Fmulder007/Karat2N_synt/1freq/tiny13synt1785/2023-01-13_09-19-21.jpg

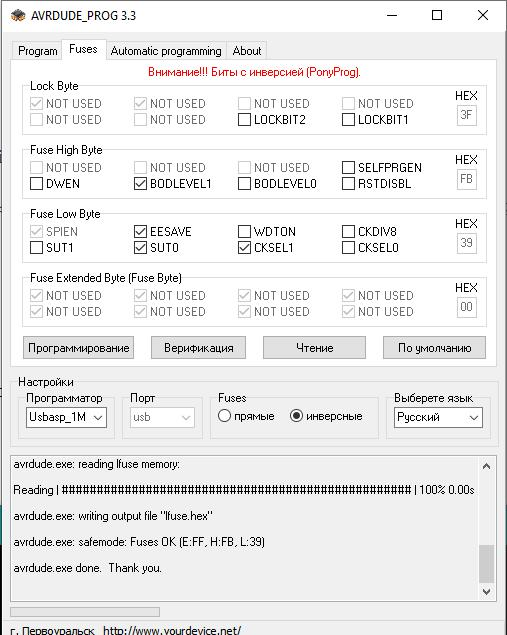
1freq/tiny13synt1785/2023-01-13_09-19-21.jpg
