Fmulder007/Karat2N_synt/3D stuff/2021-10-06_18-04-43.jpg

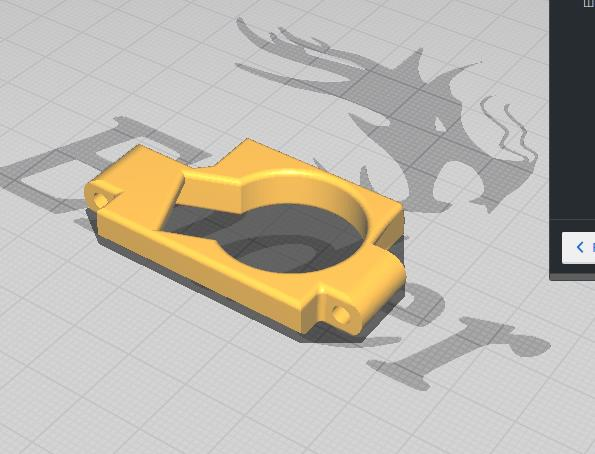
3D stuff/2021-10-06_18-04-43.jpg
