Fmulder007/Karat2N_synt/3D stuff/Conduktor.jpg

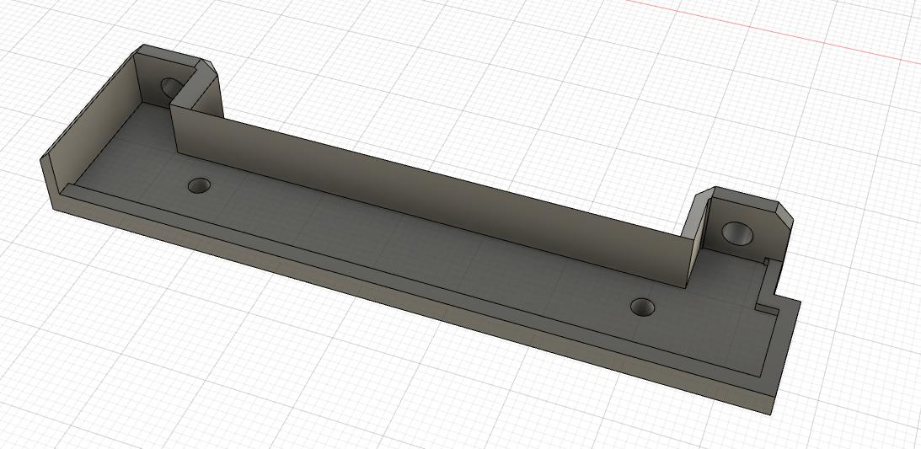
3D stuff/Conduktor.jpg
