Fmulder007/Karat2N_synt/3D stuff/photo_2021-10-07_09-59-49.jpg

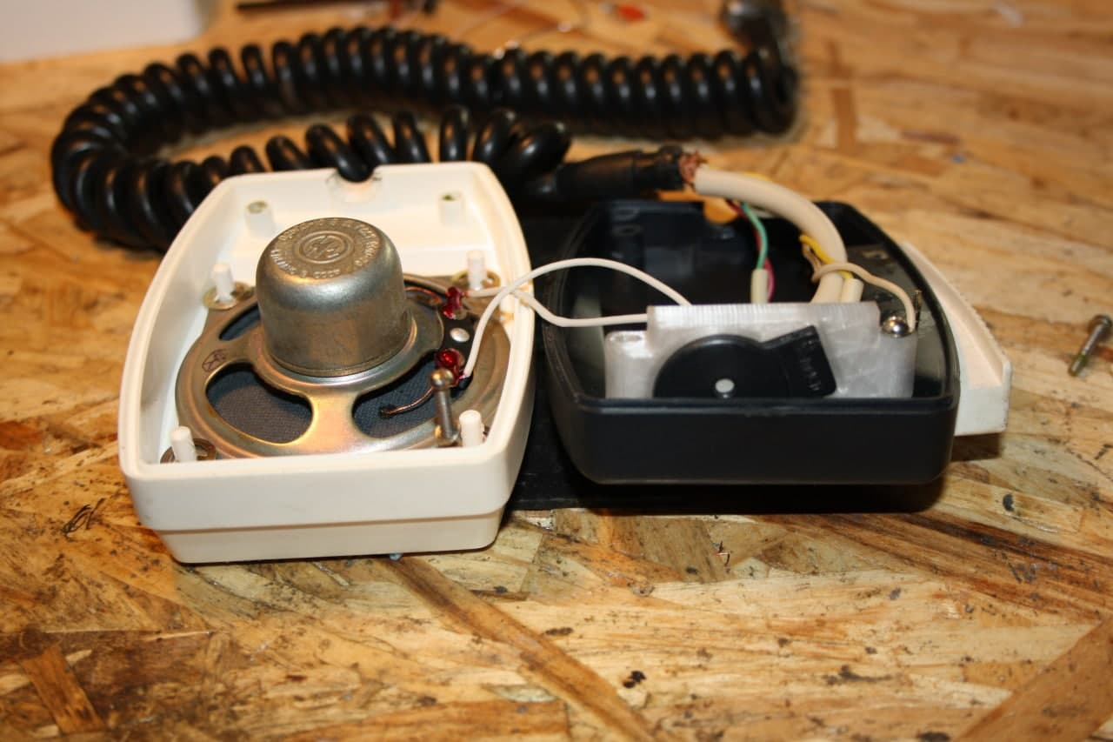
3D stuff/photo_2021-10-07_09-59-49.jpg
