Fmulder007/Karat2N_synt/3D stuff/RTC_Support.jpg

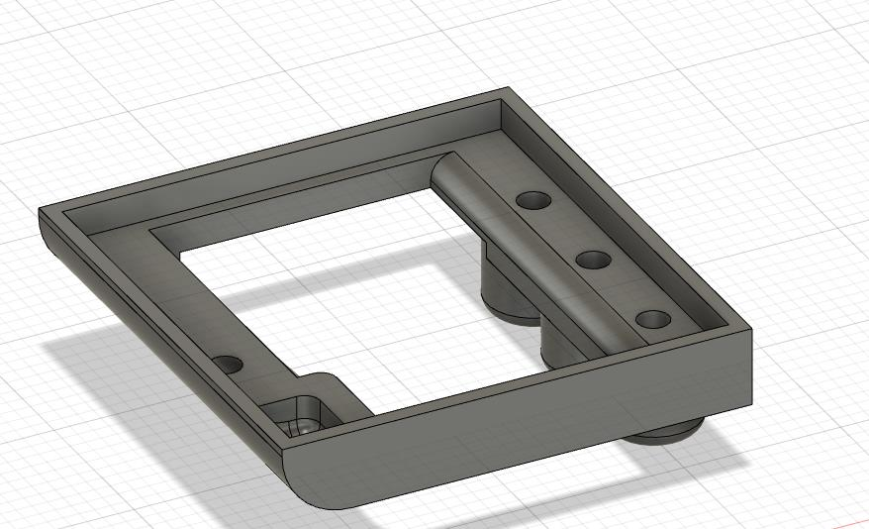
3D stuff/RTC_Support.jpg
