Fmulder007/Karat2N_synt/2021-10-20_19-13-40.jpg

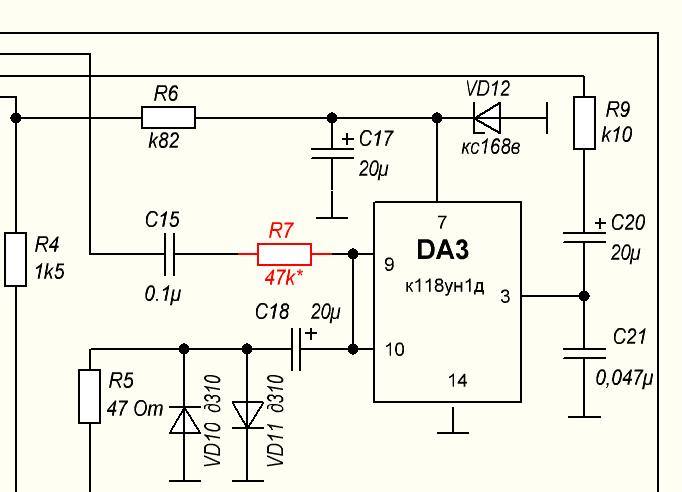
2021-10-20_19-13-40.jpg
