Fmulder007/Karat2N_synt/2021-10-20_19-15-04.jpg

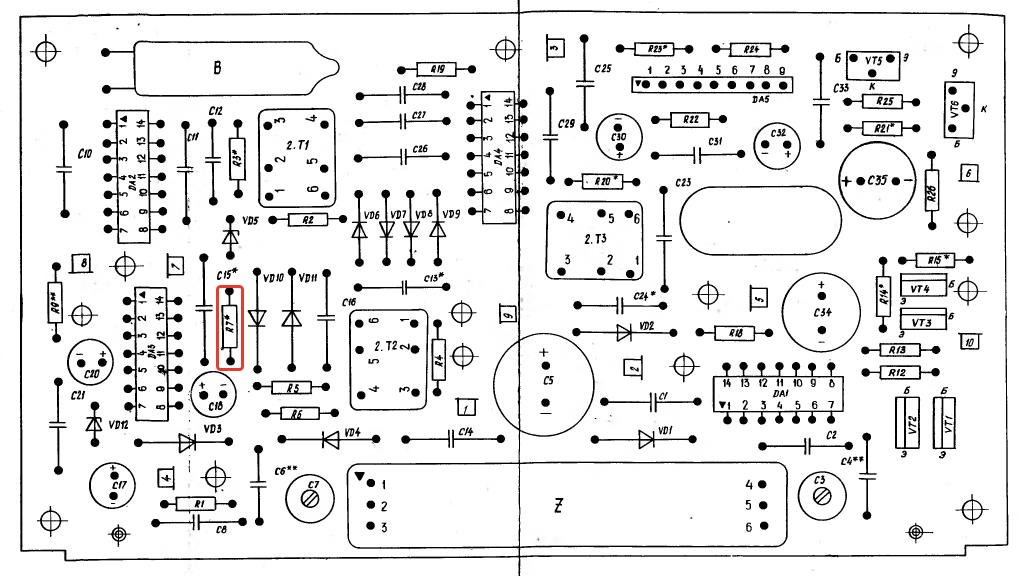
2021-10-20_19-15-04.jpg
