Fmulder007/Karat2N_synt/2022-11-13_21-02-55.jpg

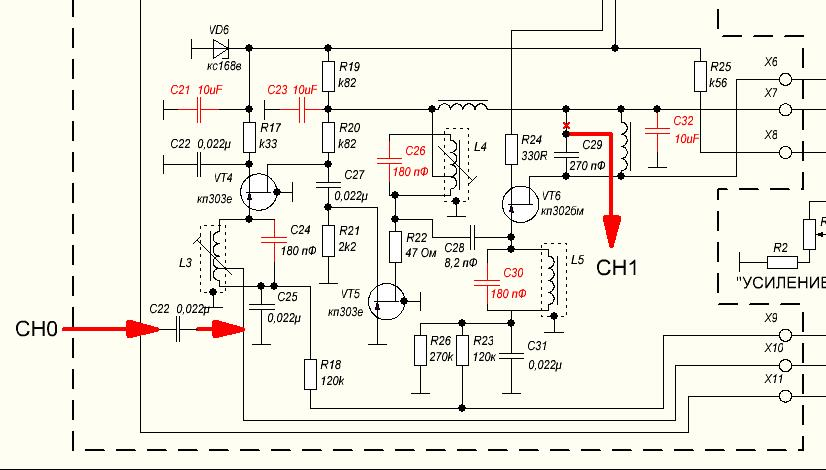
2022-11-13_21-02-55.jpg
