Fmulder007/Karat2N_synt/ANT.GIF

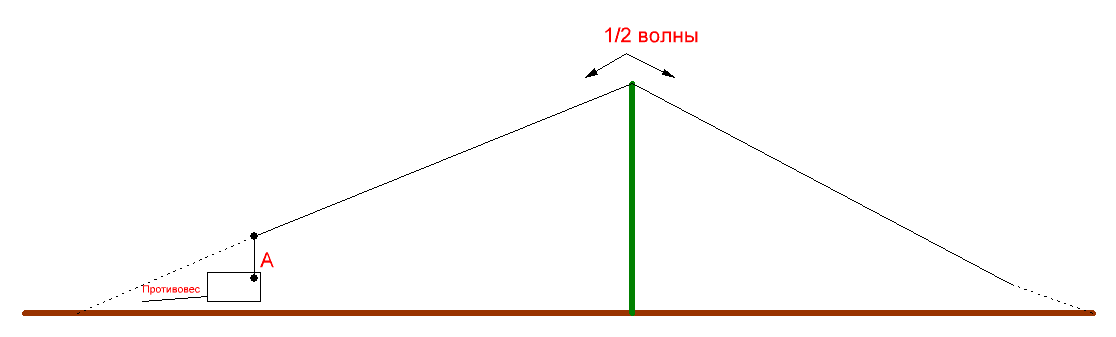
ANT.GIF
