Fmulder007/Karat2N_synt/DEMSH.GIF

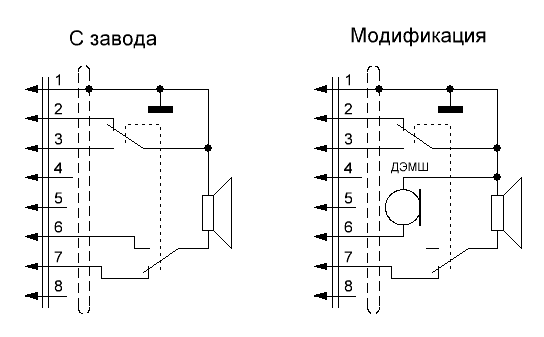
DEMSH.GIF
