Fmulder007/Karat2N_synt/Driver.GIF

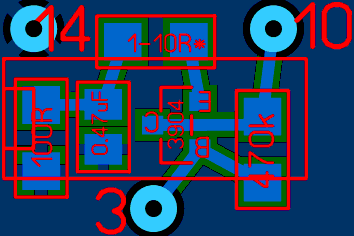
Driver.GIF
