Fmulder007/Karat2N_synt/DriverSch.GIF

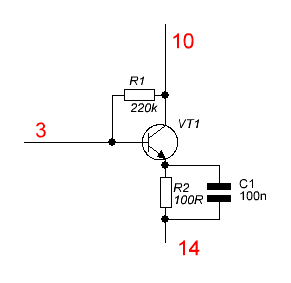
DriverSch.GIF
