Fmulder007/Karat2N_synt/Karat-2N_New_A1.GIF

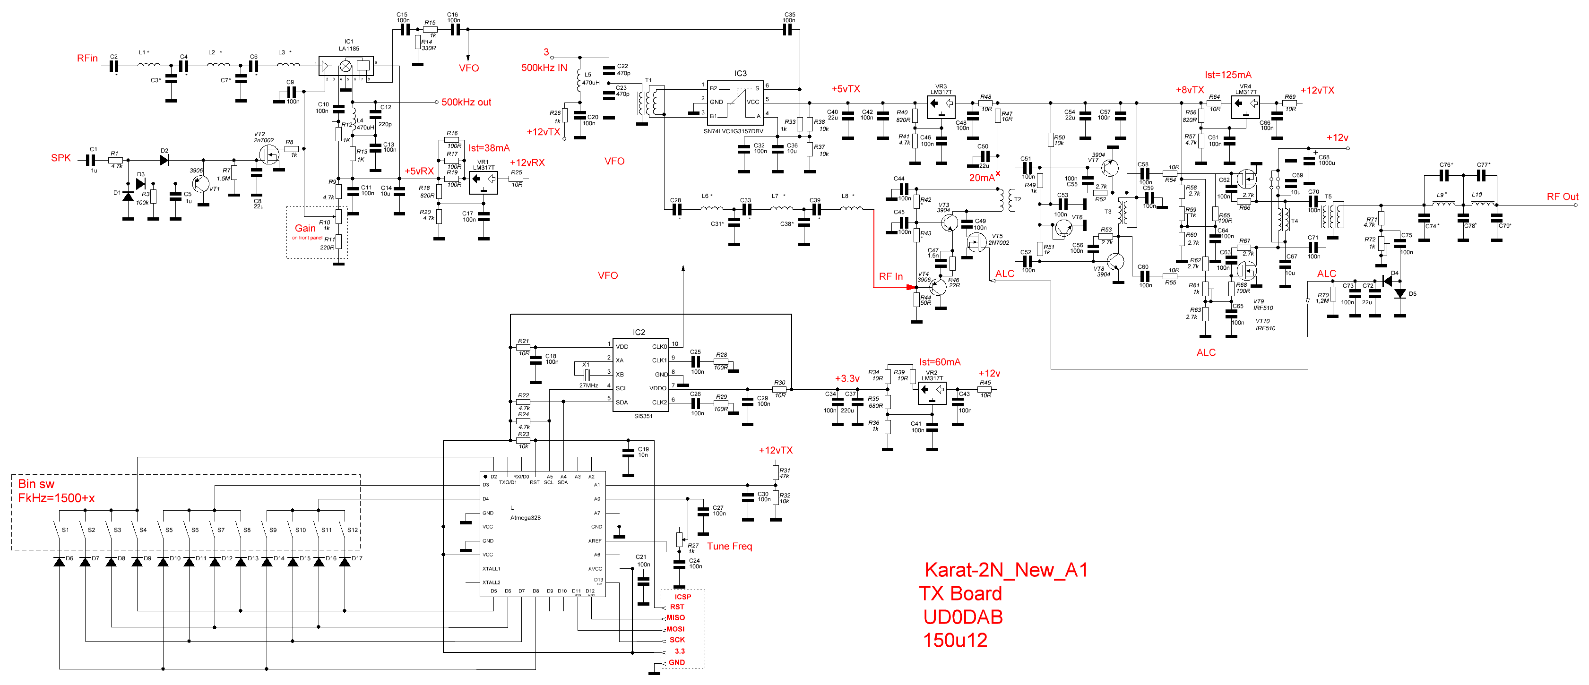
Karat-2N_New_A1.GIF
