Fmulder007/Karat2N_synt/Karat_Sintez328.GIF

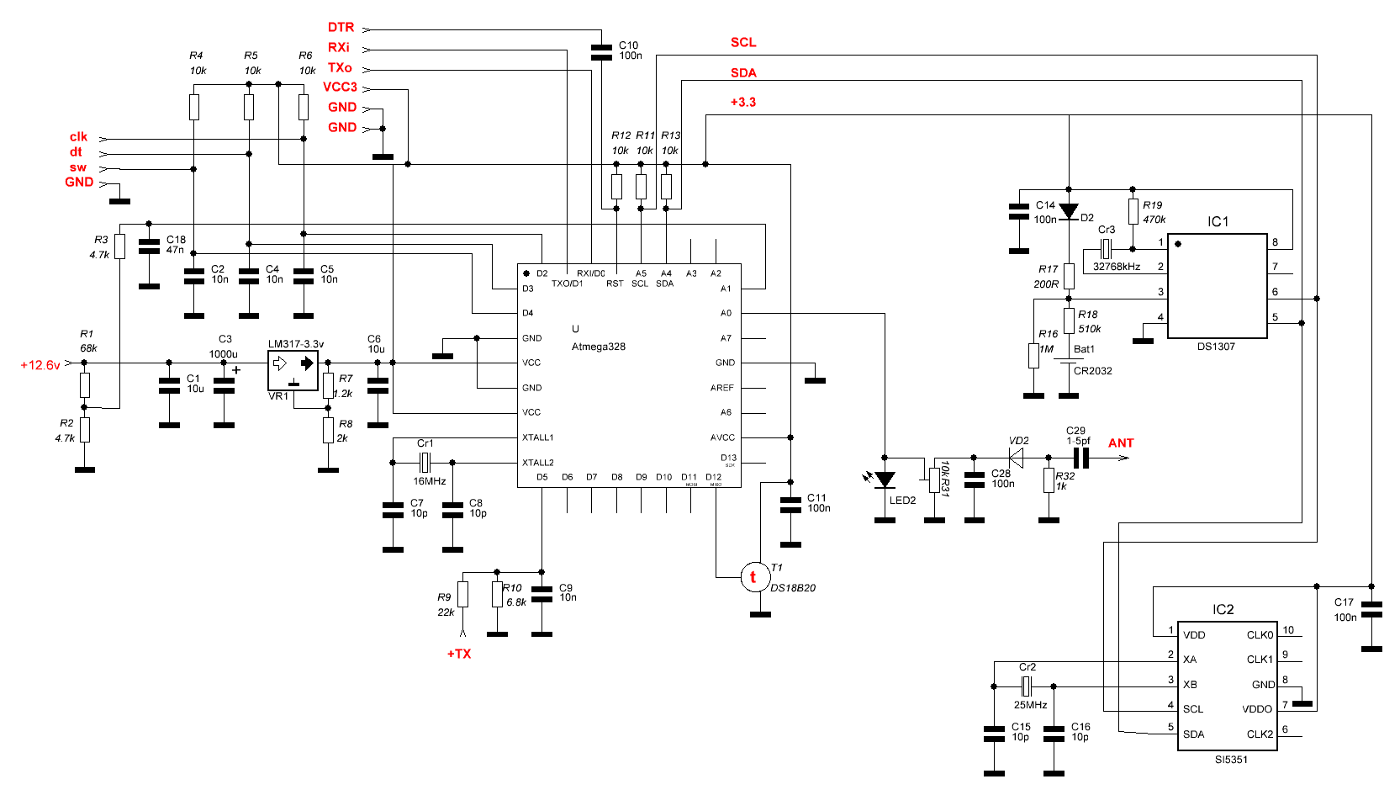
Karat_Sintez328.GIF
