Fmulder007/Karat2N_synt/Karat_Sintez328_130u02.GIF

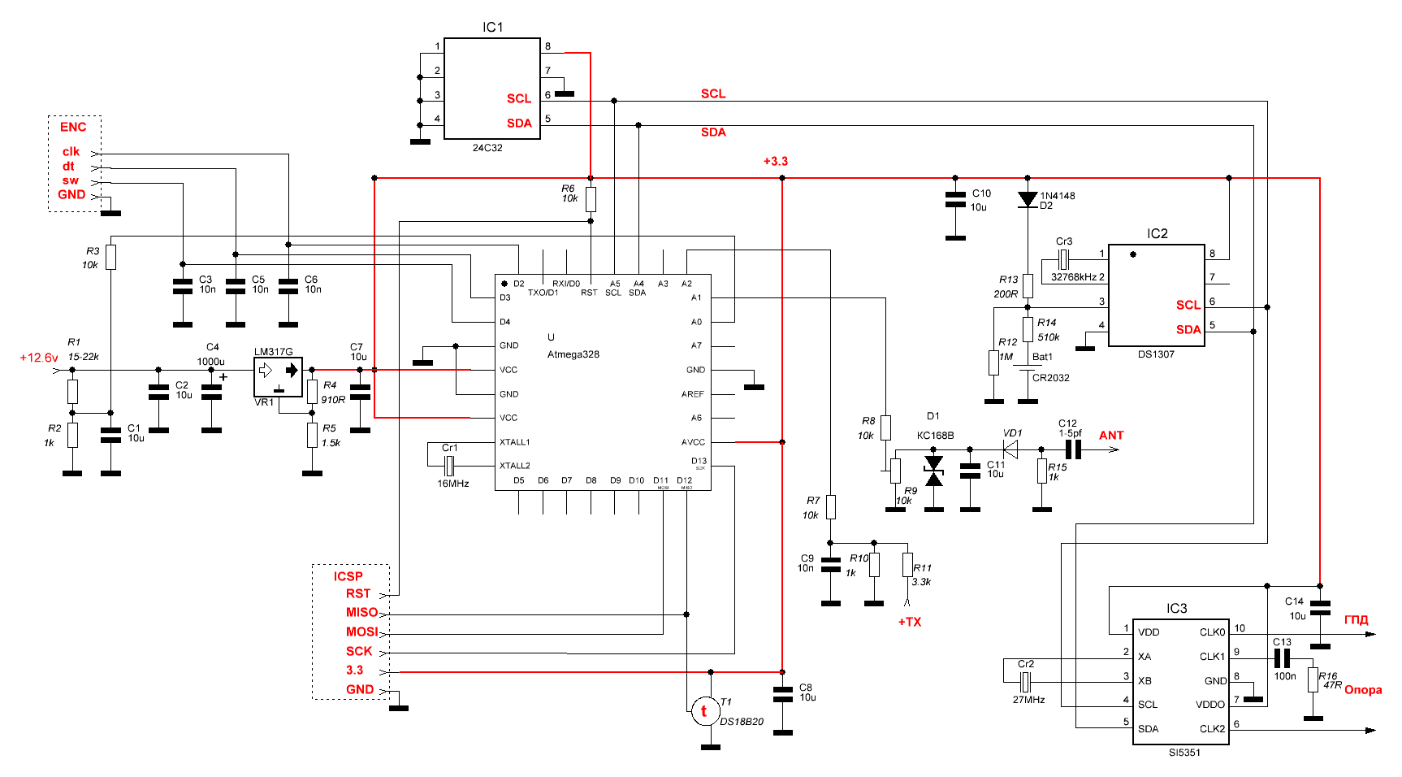
Karat_Sintez328_130u02.GIF
