Fmulder007/Karat2N_synt/Karat_SintezArduino.GIF

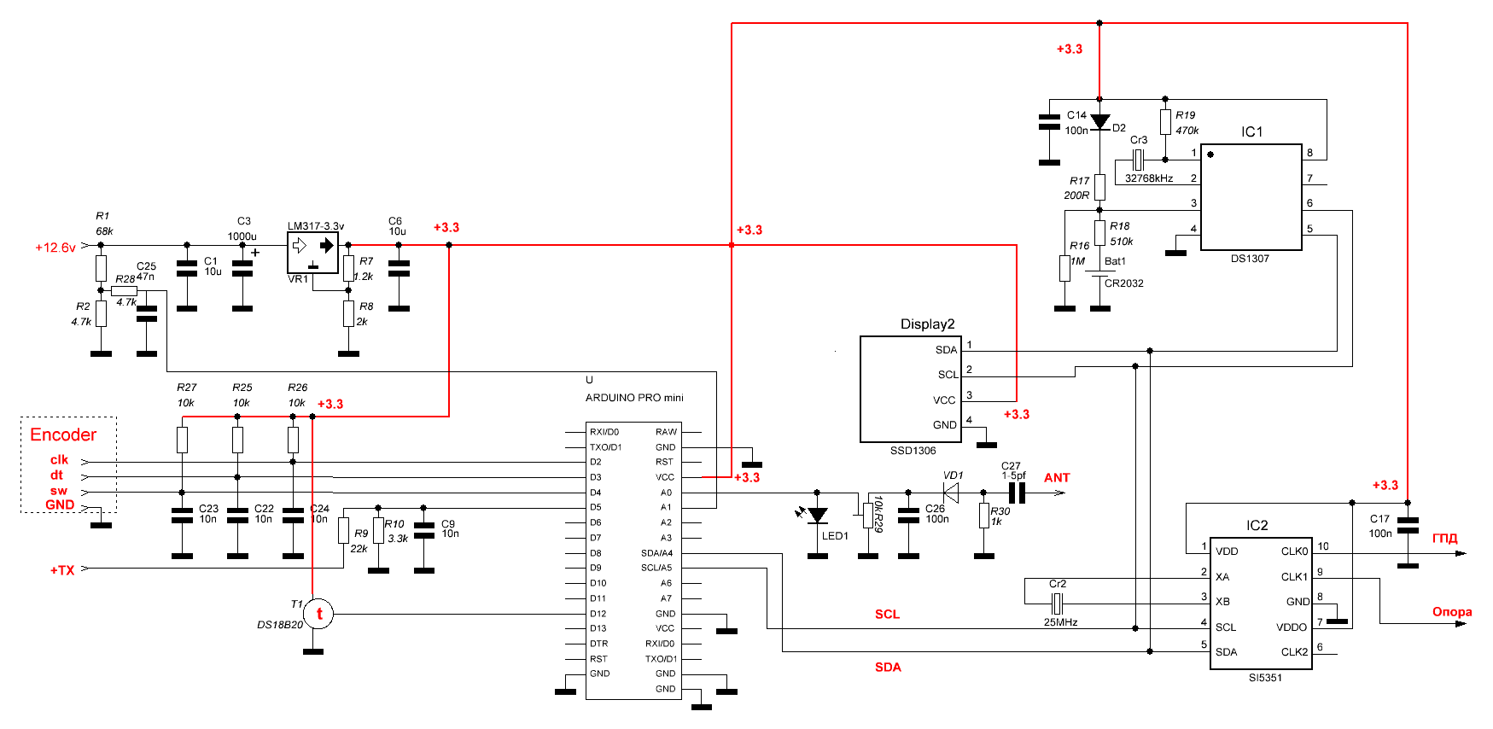
Karat_SintezArduino.GIF
