Fmulder007/Karat2N_synt/Karat_SintezArduino_130u02.GIF

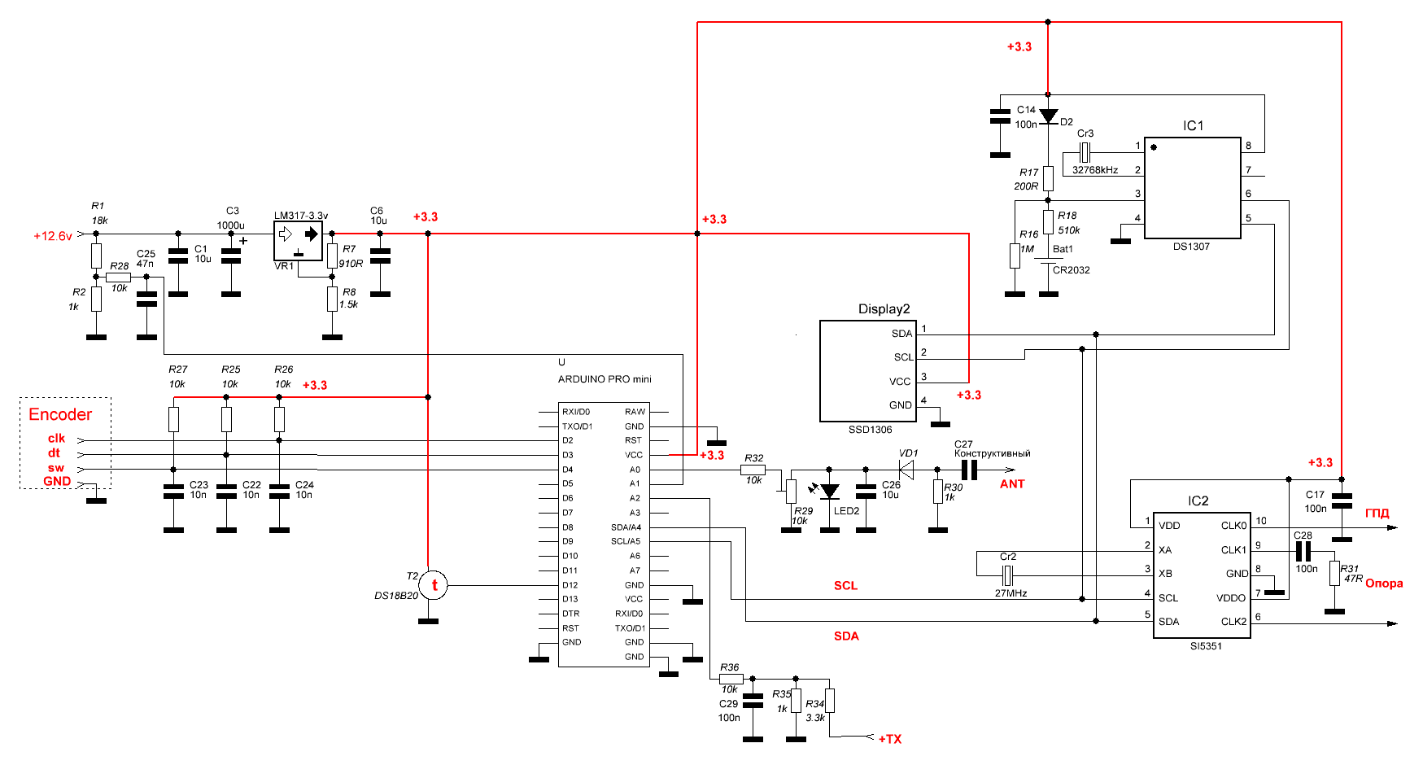
Karat_SintezArduino_130u02.GIF
