Fmulder007/Karat2N_synt/PA1.GIF

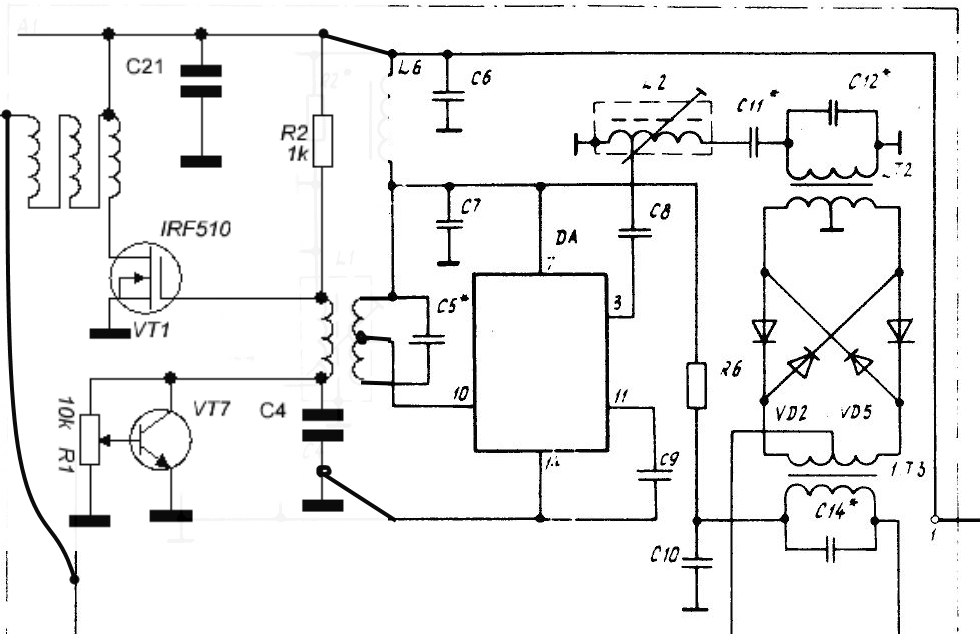
PA1.GIF
