Fmulder007/Karat2N_synt/PA.GIF

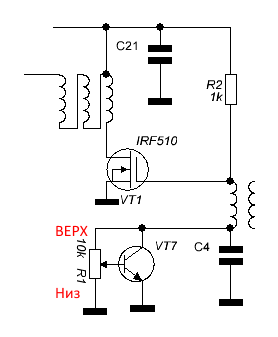
PA.GIF
