Fmulder007/Karat2N_synt/Photo/40m_receiver_coils.jpg

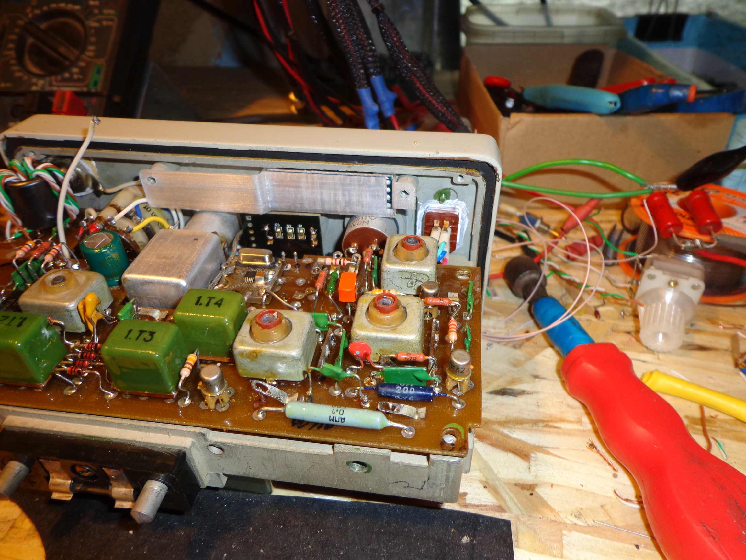
Photo/40m_receiver_coils.jpg
