Fmulder007/Karat2N_synt/Photo/Display_acrylic_shield.jpg

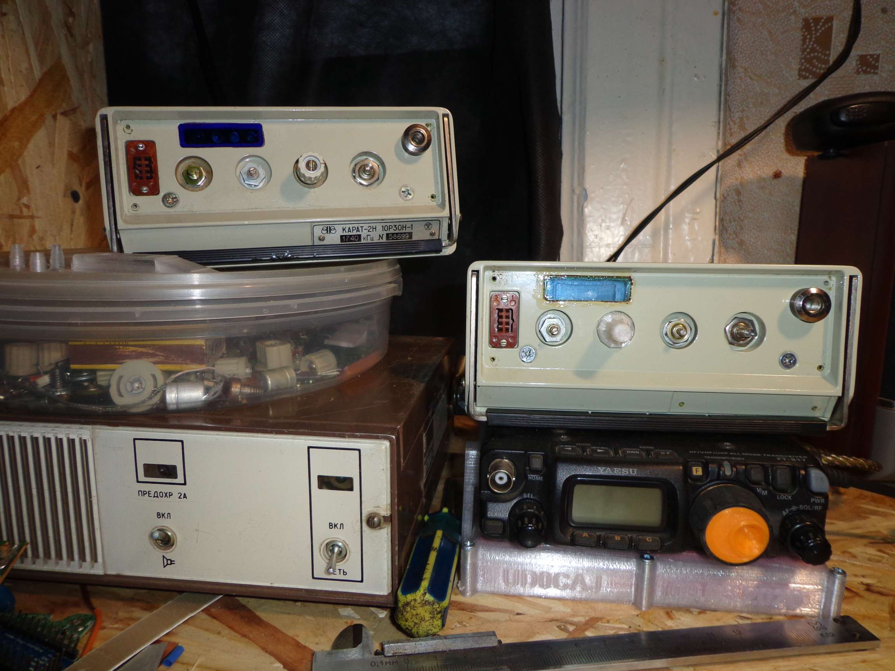
Photo/Display_acrylic_shield.jpg
