Fmulder007/Karat2N_synt/Photo/DSC01830.jpg

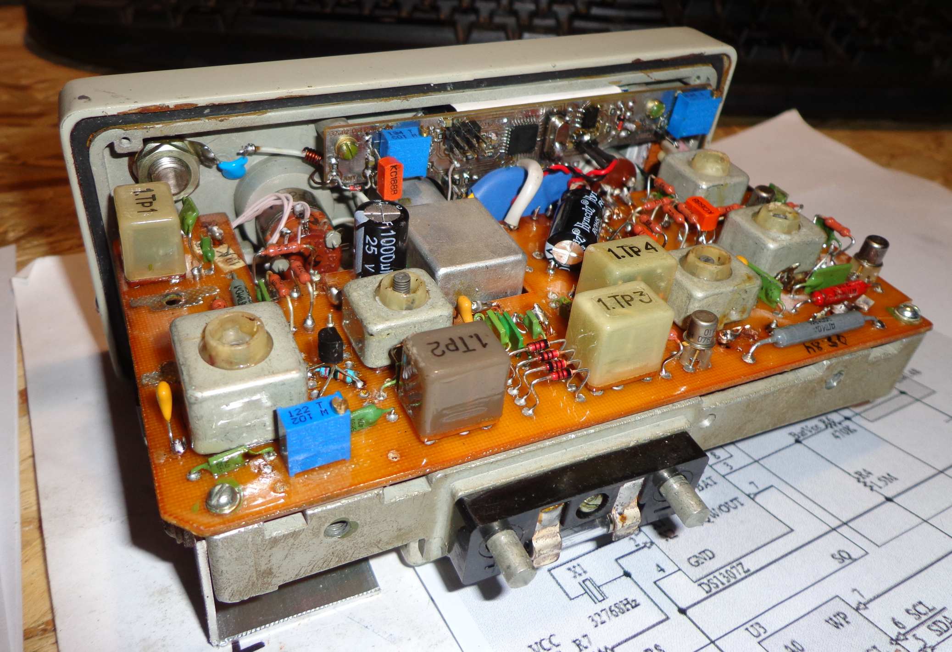
Photo/DSC01830.jpg
