Fmulder007/Karat2N_synt/Photo/DSC01836.jpg

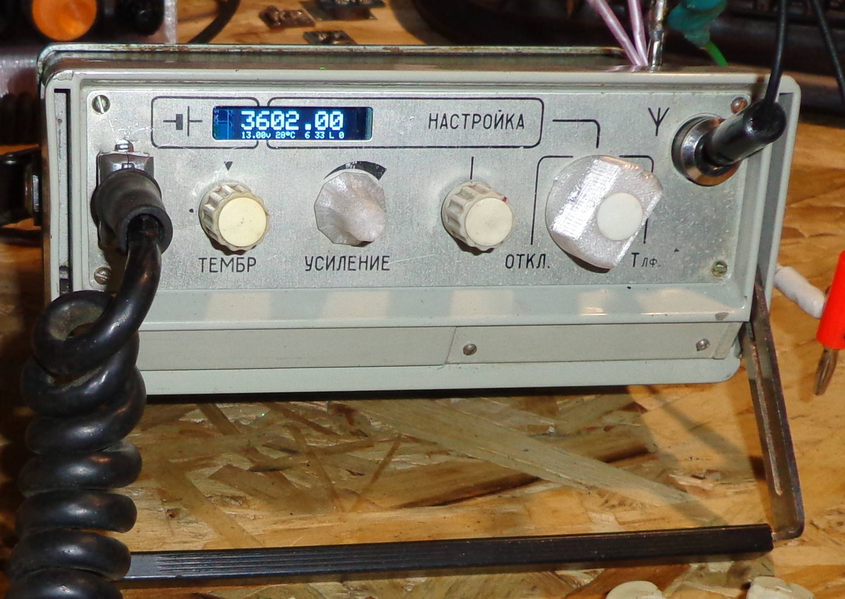
Photo/DSC01836.jpg
