Fmulder007/Karat2N_synt/Photo/IMG_2728.jpg

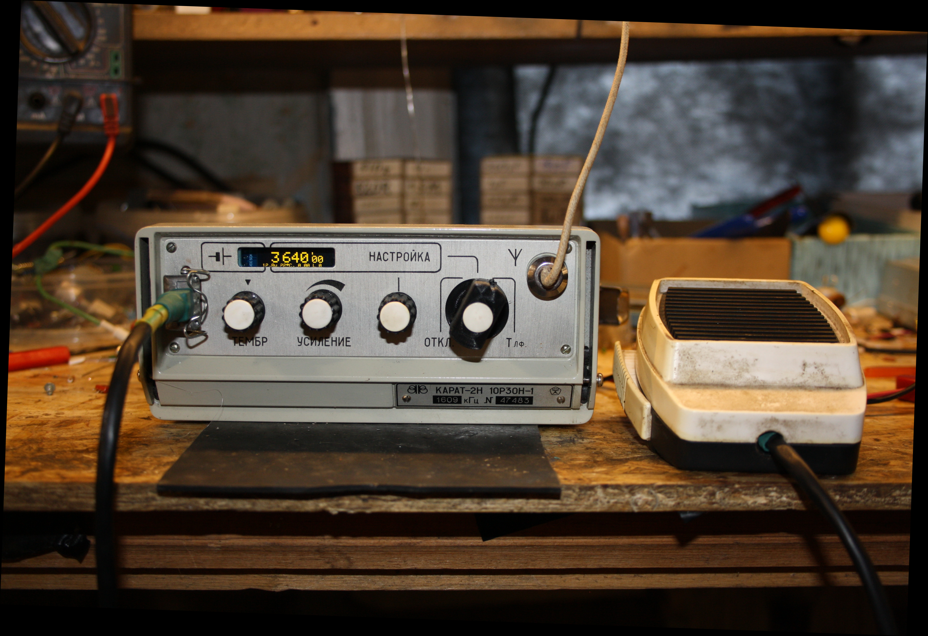
Photo/IMG_2728.jpg
