Fmulder007/Karat2N_synt/Photo/IMG_2859.JPG

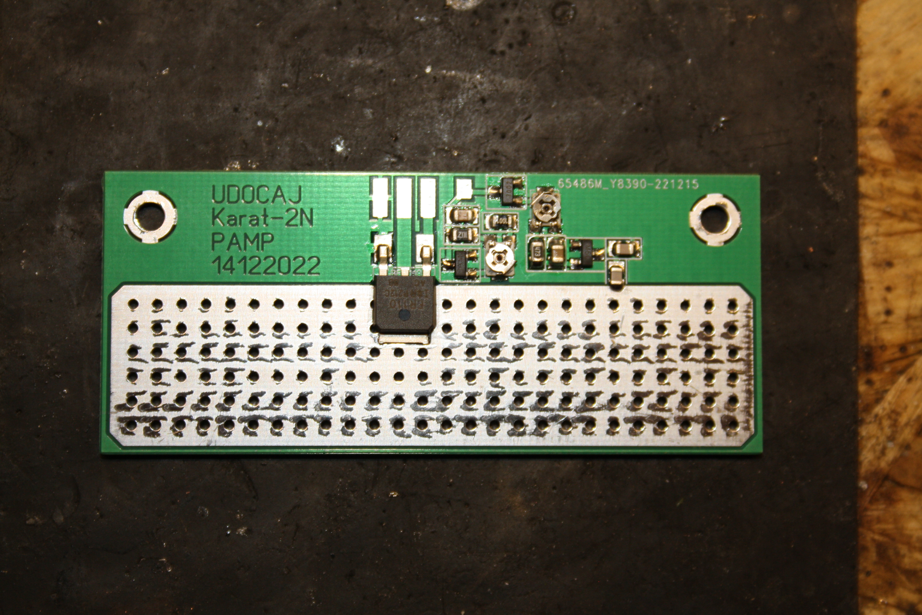
Photo/IMG_2859.JPG
