Fmulder007/Karat2N_synt/Photo/IMG_20241121_151414_054.jpg

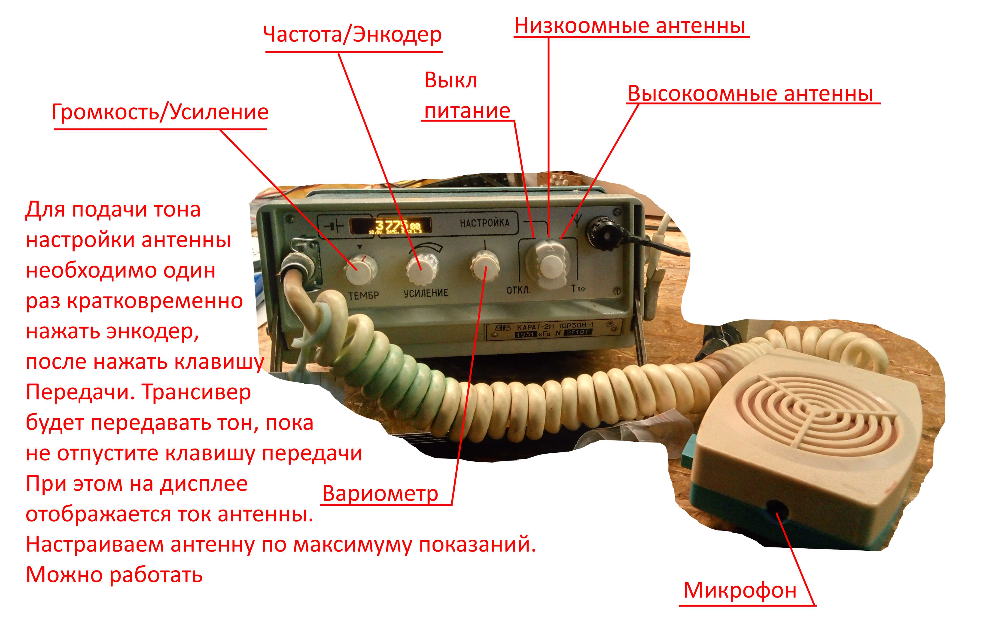
Photo/IMG_20241121_151414_054.jpg
