Fmulder007/Karat2N_synt/Photo/Original.jpg

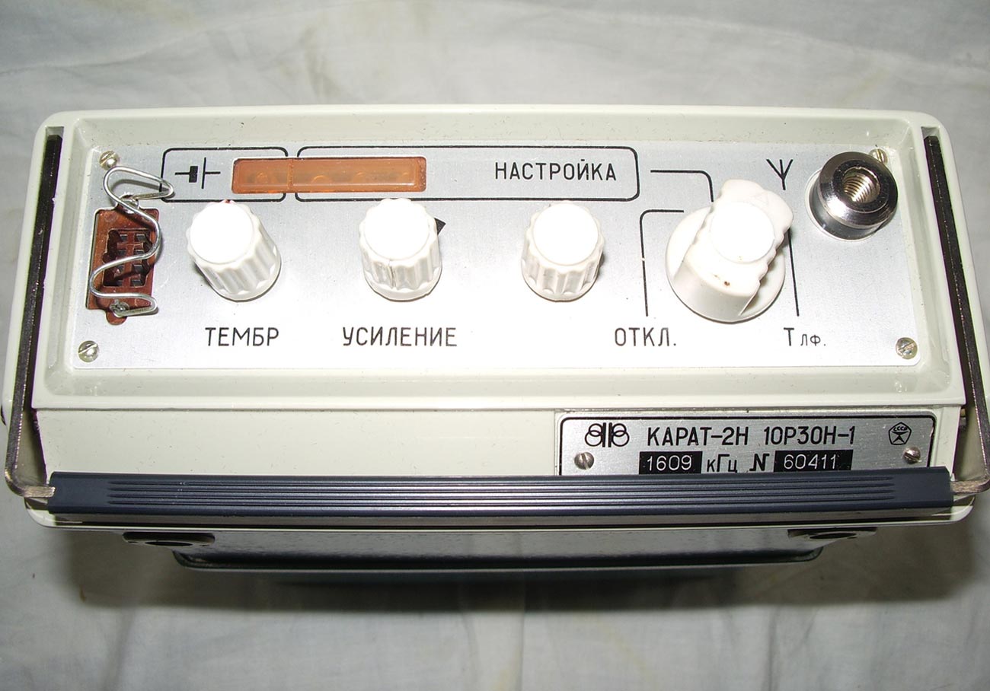
Photo/Original.jpg
