Fmulder007/Karat2N_synt/Photo/photo_2020-11-11_01-21-56.jpg

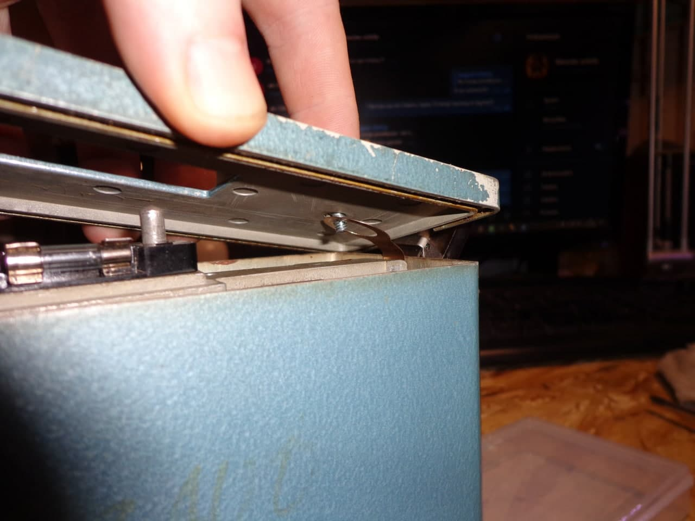
Photo/photo_2020-11-11_01-21-56.jpg
