Fmulder007/Karat2N_synt/Photo/photo_2020-11-11_01-22-02.jpg

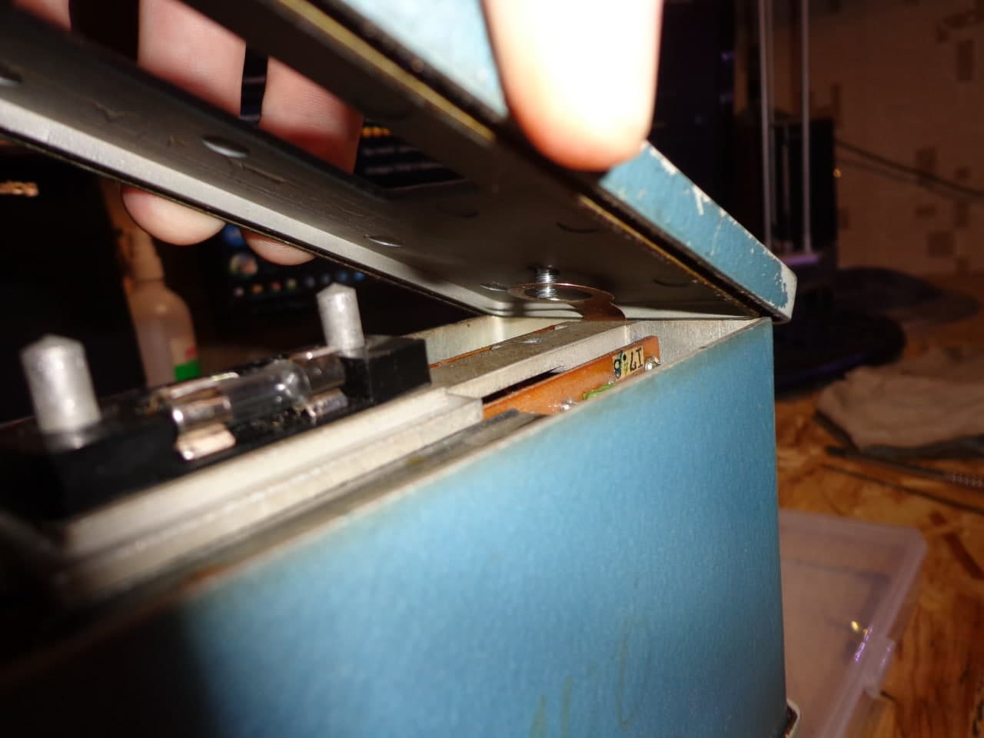
Photo/photo_2020-11-11_01-22-02.jpg
