Fmulder007/Karat2N_synt/Photo/photo_2020-11-12_05-07-51.jpg

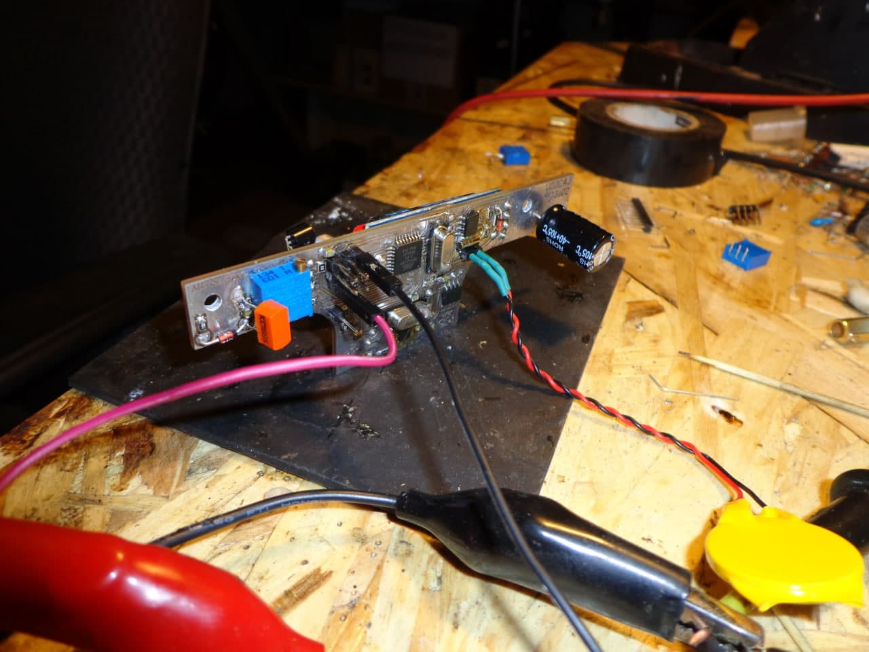
Photo/photo_2020-11-12_05-07-51.jpg
