Fmulder007/Karat2N_synt/Photo/photo_2021-01-18_15-01-44.jpg

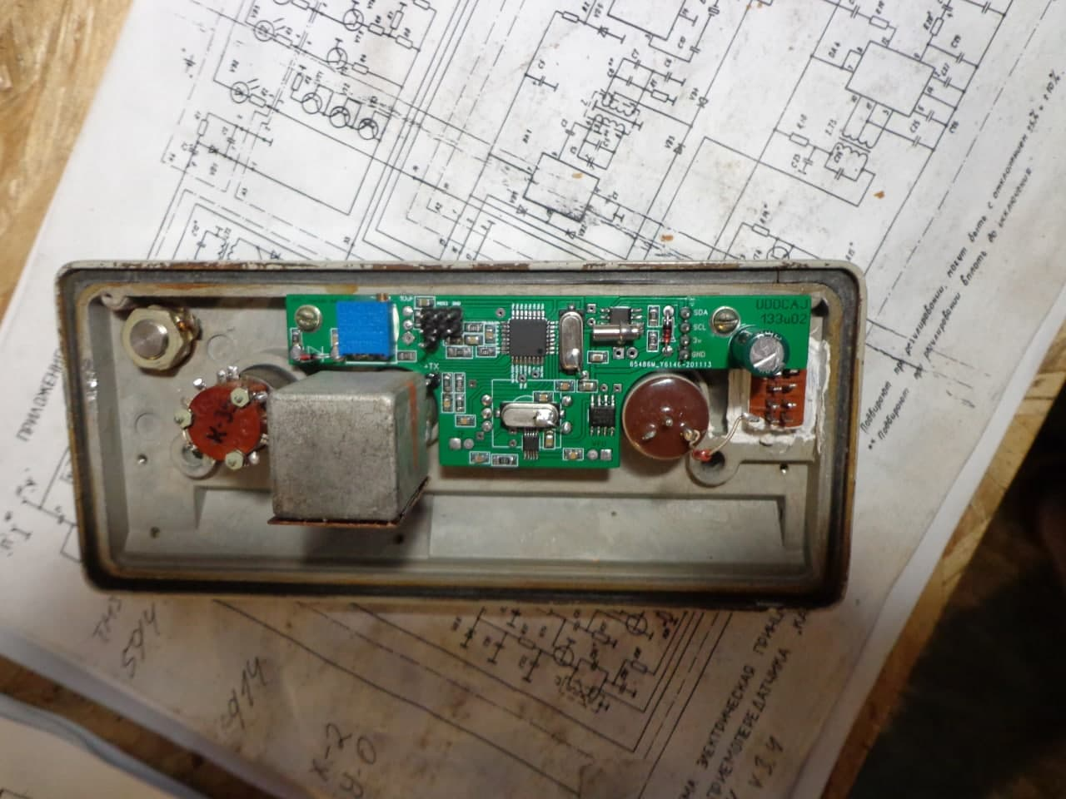
Photo/photo_2021-01-18_15-01-44.jpg
