Fmulder007/Karat2N_synt/Photo/photo_2021-02-04_23-26-35.jpg

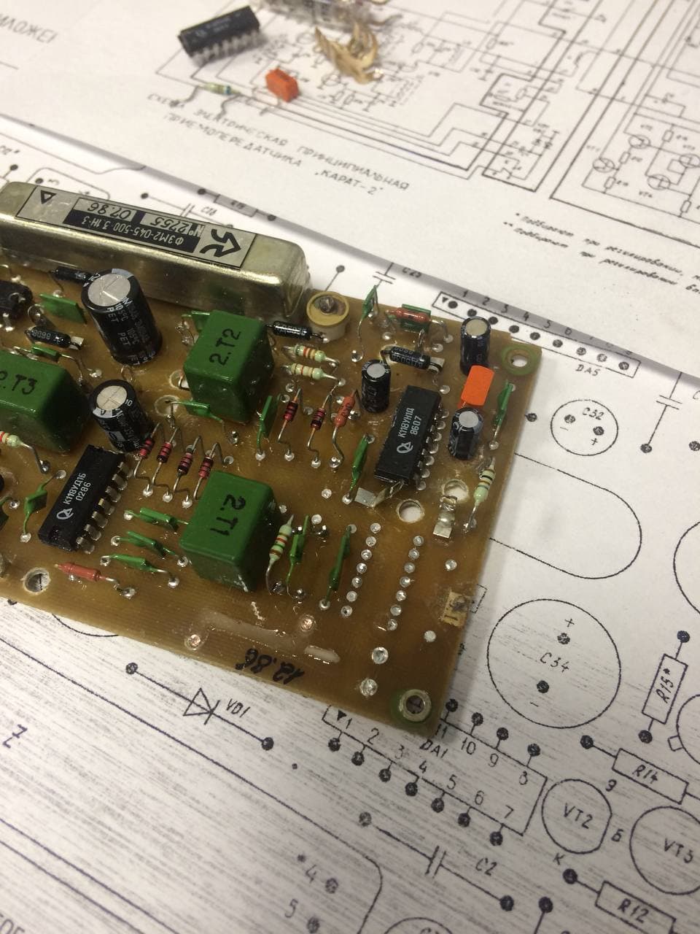
Photo/photo_2021-02-04_23-26-35.jpg
