Fmulder007/Karat2N_synt/Photo/photo_2021-03-17_01-12-06.jpg

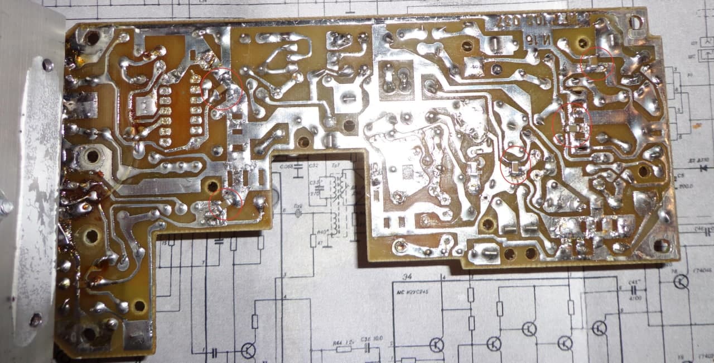
Photo/photo_2021-03-17_01-12-06.jpg
