Fmulder007/Karat2N_synt/Photo/photo_2022-10-07_20-26-55.jpg

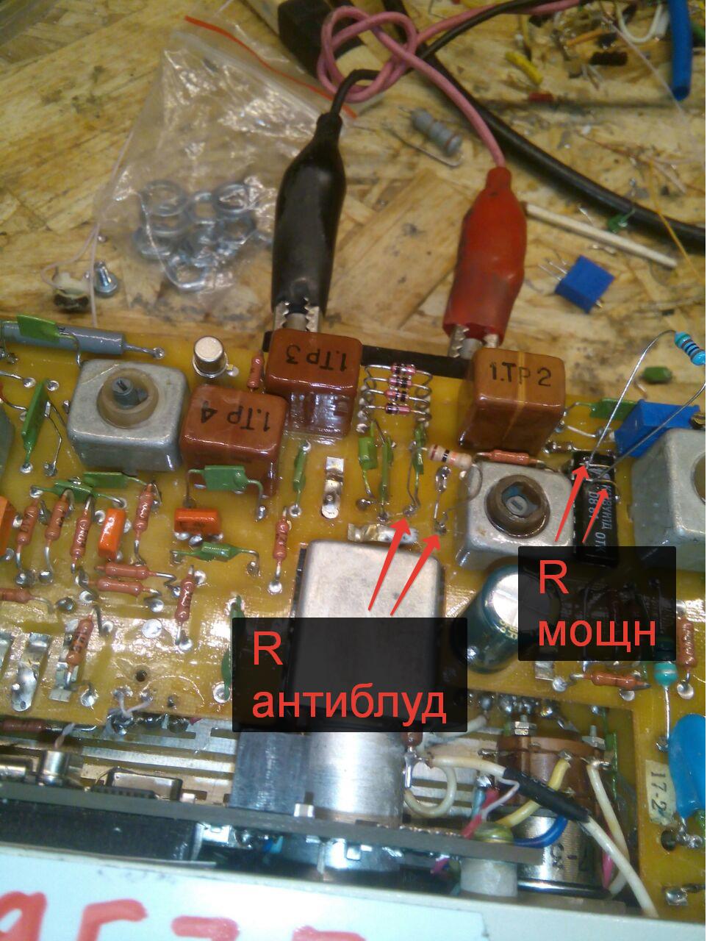
Photo/photo_2022-10-07_20-26-55.jpg
