Fmulder007/Karat2N_synt/Photo/photo_2022-12-13_17-33-09.jpg

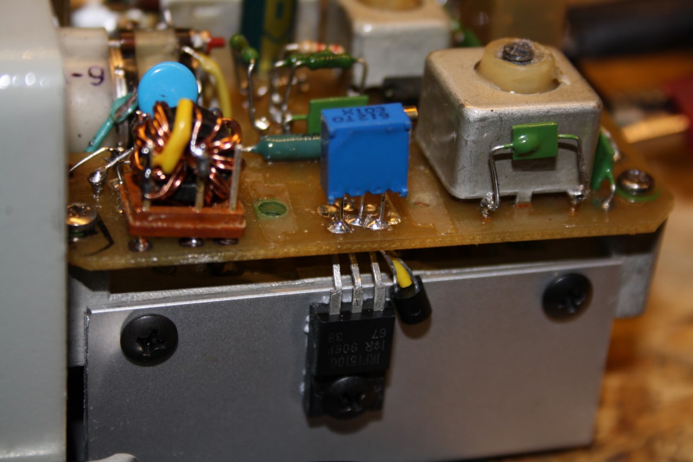
Photo/photo_2022-12-13_17-33-09.jpg
