Fmulder007/Karat2N_synt/Photo/photo_2022-12-13_17-33-28.jpg

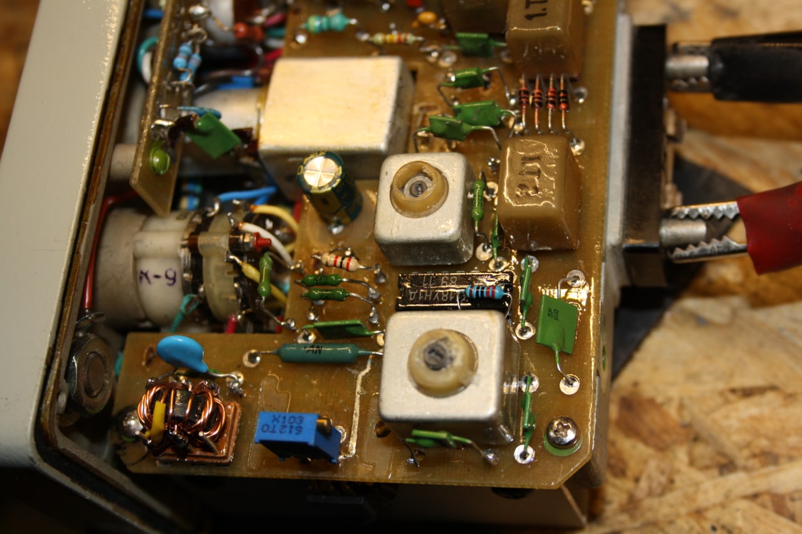
Photo/photo_2022-12-13_17-33-28.jpg
