Fmulder007/Karat2N_synt/Photo/Upgraded000.jpg

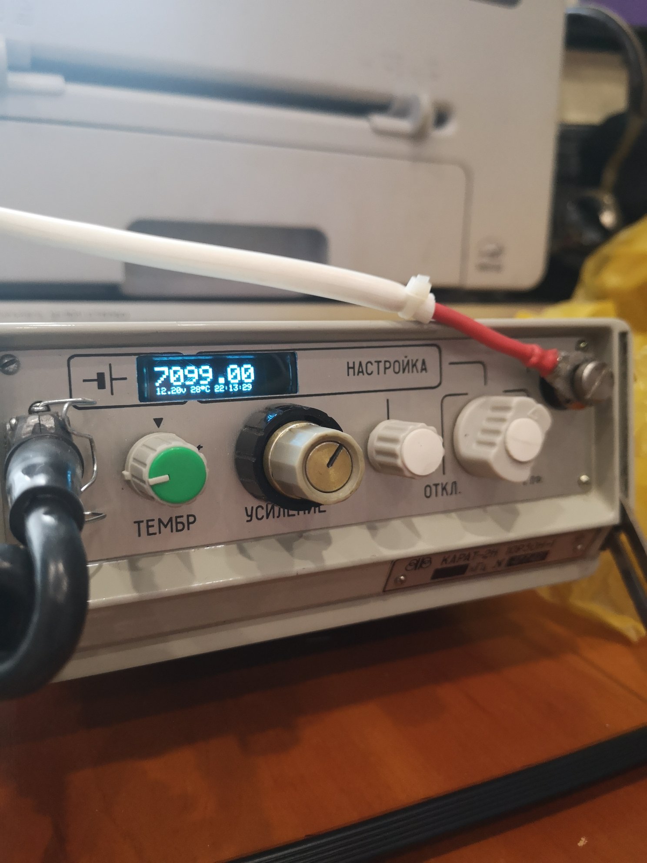
Photo/Upgraded000.jpg
