Fmulder007/Karat2N_synt/Photo/Upgraded001.jpg

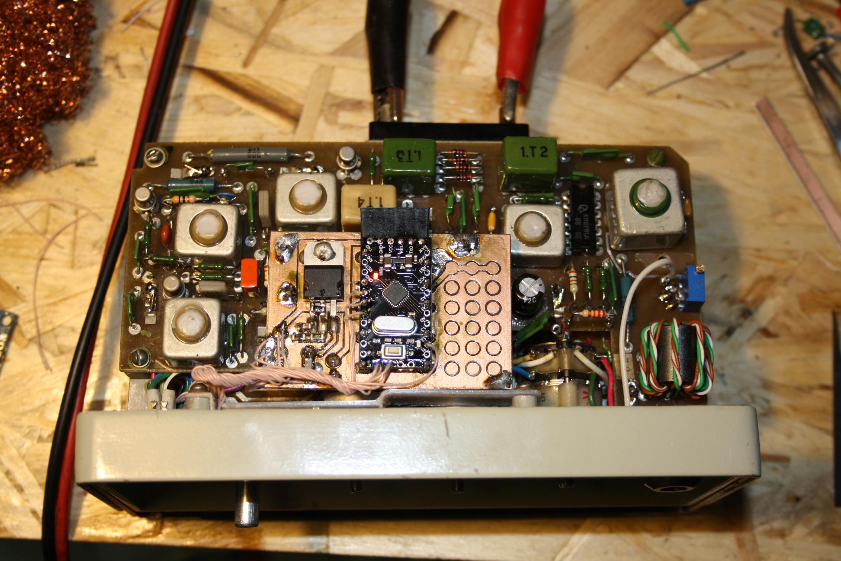
Photo/Upgraded001.jpg
