Fmulder007/Karat2N_synt/Photo/Upgraded002.jpg

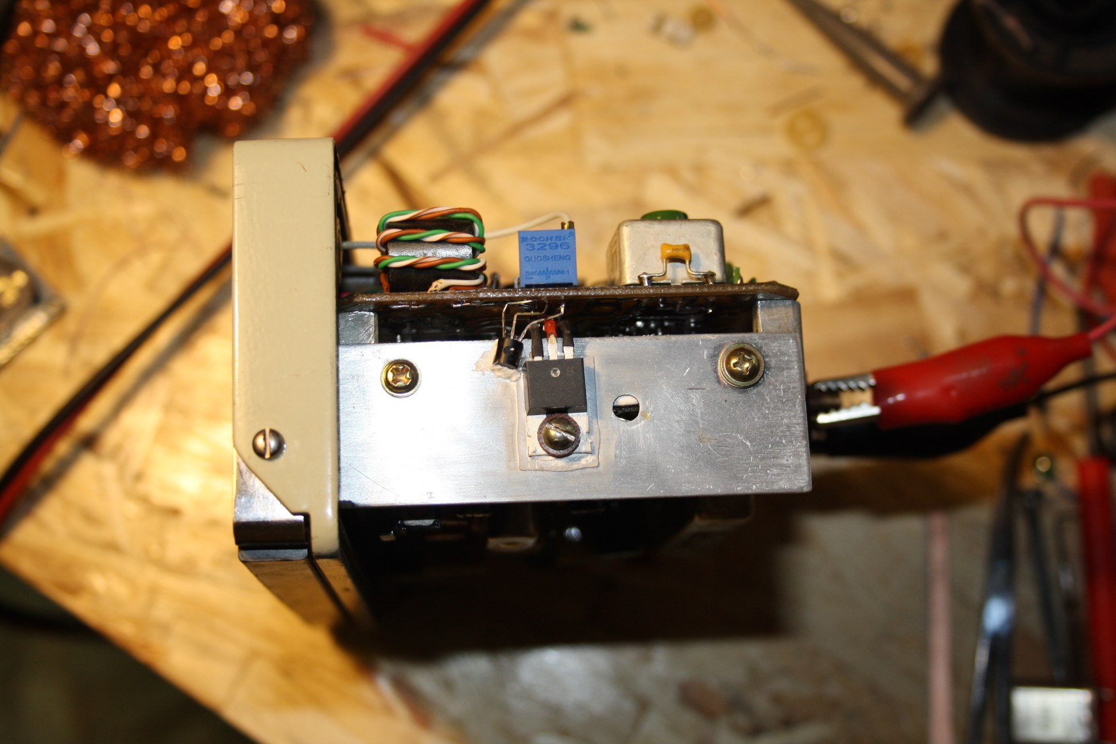
Photo/Upgraded002.jpg
