Fmulder007/Karat2N_synt/Photo/Upgraded003.jpg

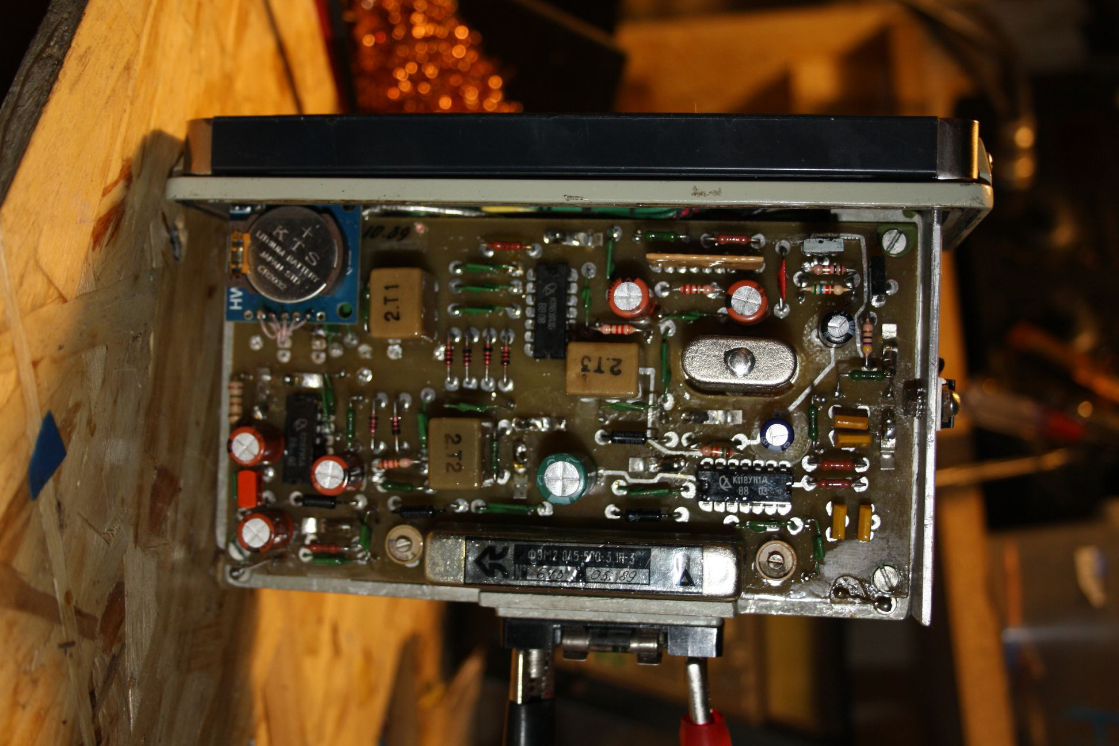
Photo/Upgraded003.jpg
