Fmulder007/Karat2N_synt/Photo/Upgraded004.jpg

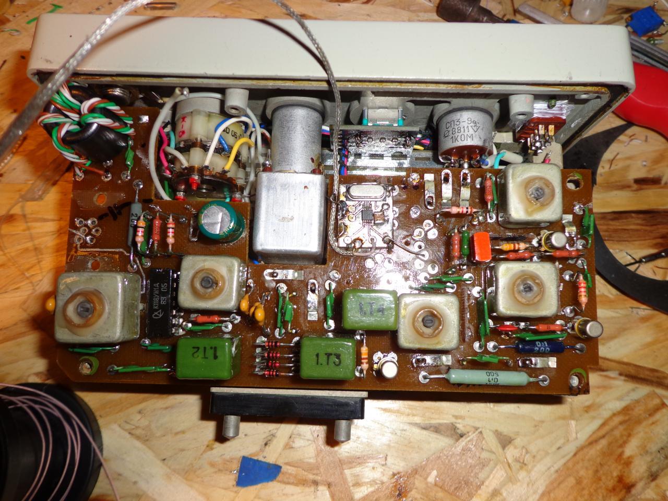
Photo/Upgraded004.jpg
