Fmulder007/Karat2N_synt/Photo/Upgraded005.jpg

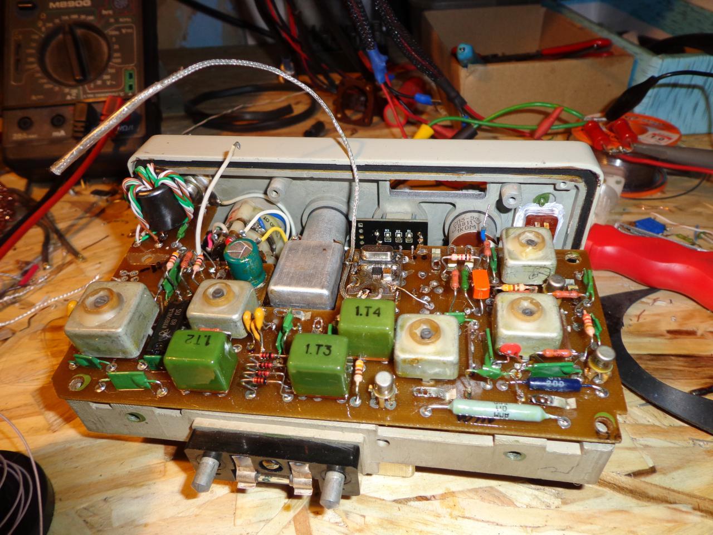
Photo/Upgraded005.jpg
