Fmulder007/Karat2N_synt/Splan/Sintez150x12.jpg

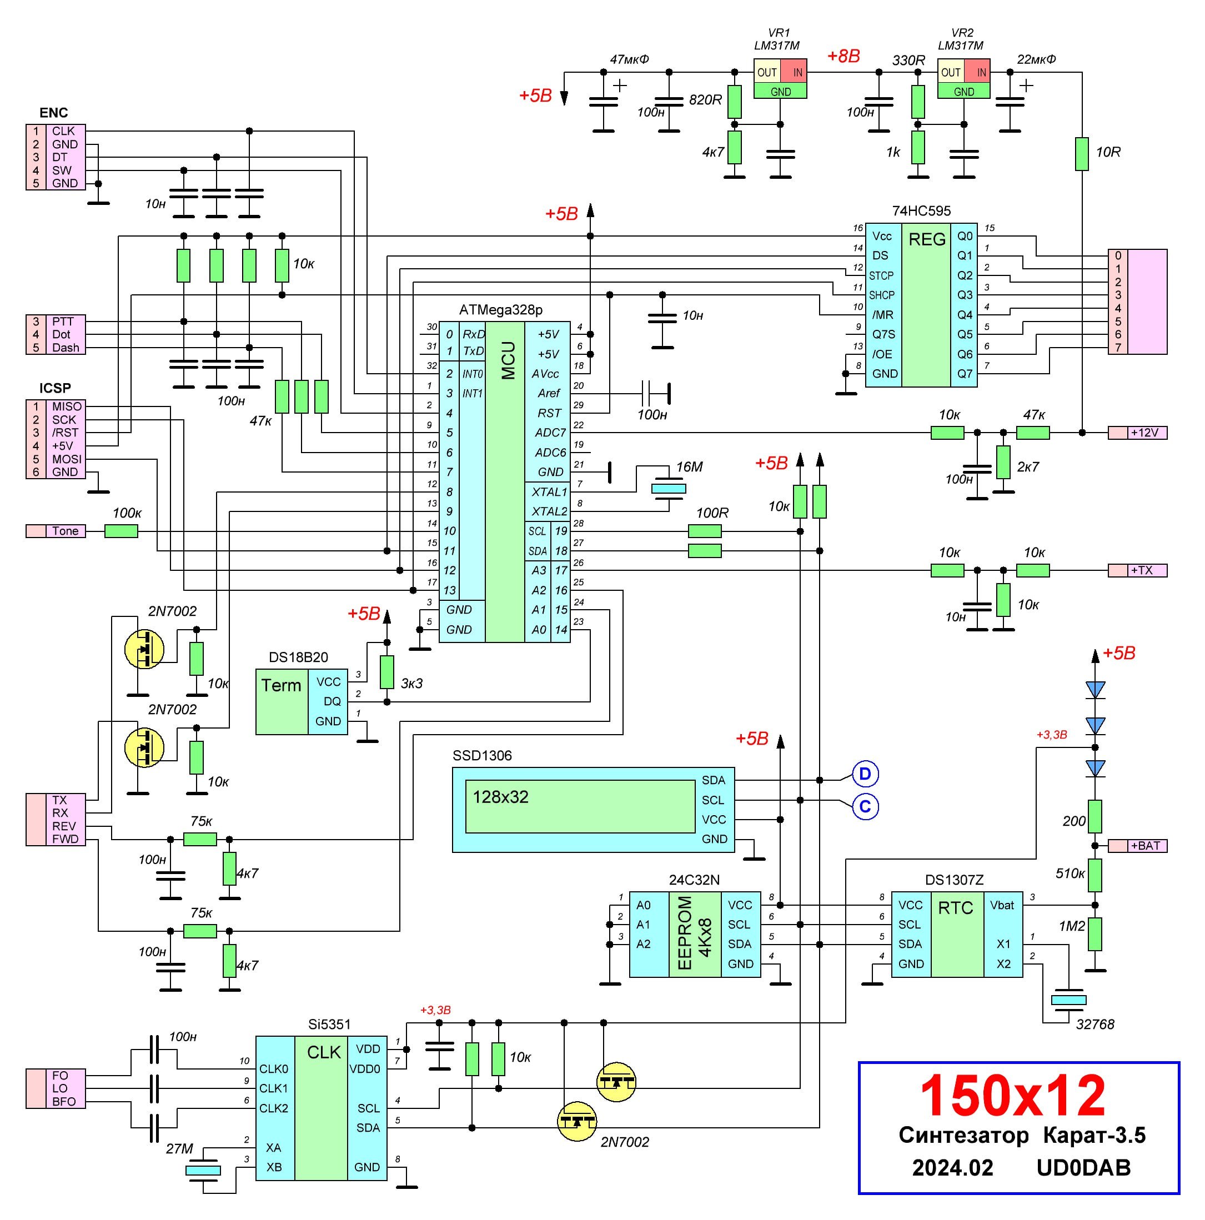
Splan/Sintez150x12.jpg
