Fmulder007/Karat2N_synt/VFO_AMP.GIF

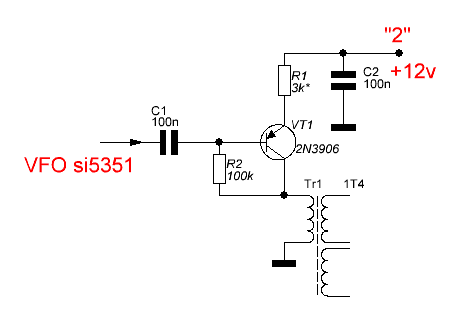
VFO_AMP.GIF
