Fmulder007/Karat2N_synt/Антиблуд при умощнении.GIF

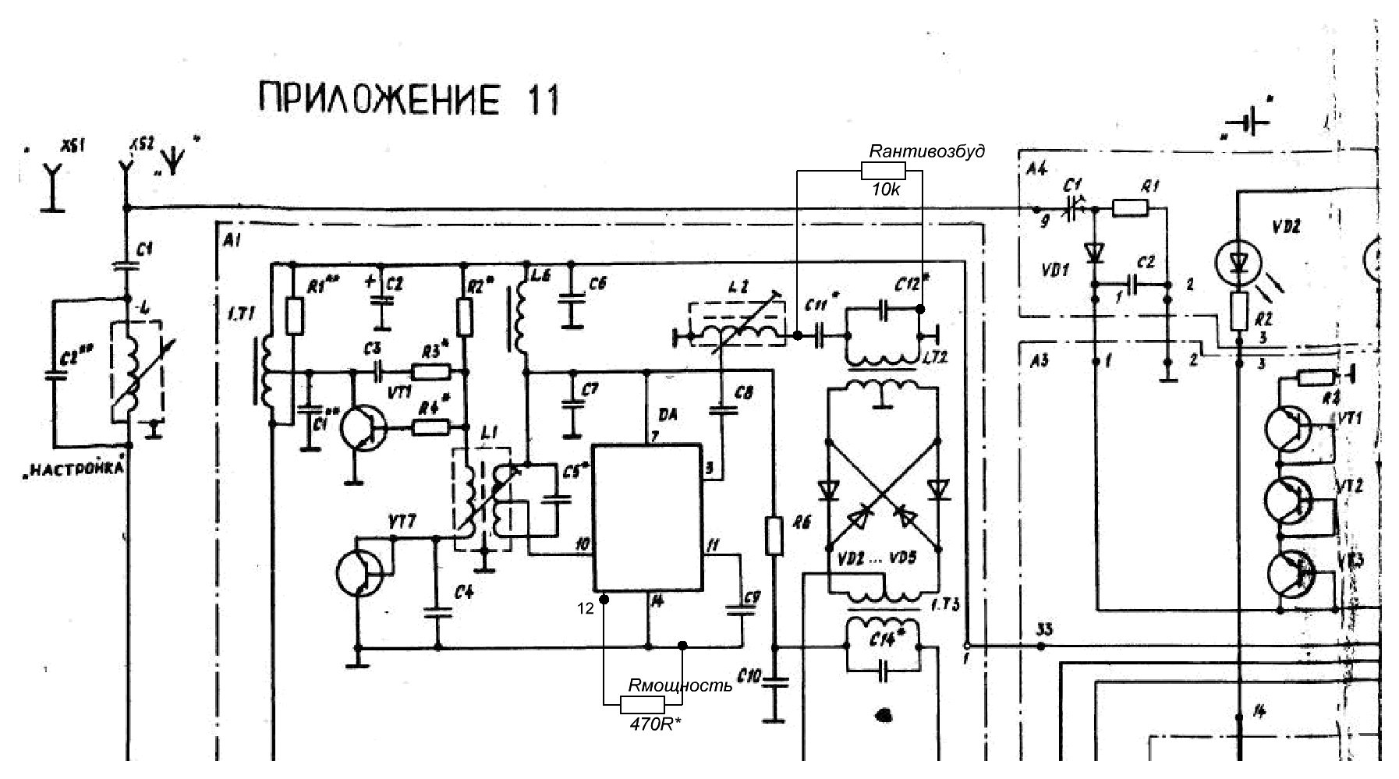
Антиблуд при умощнении.GIF
