Fmulder007/Karat2N_synt/3D stuff/Torus.stl

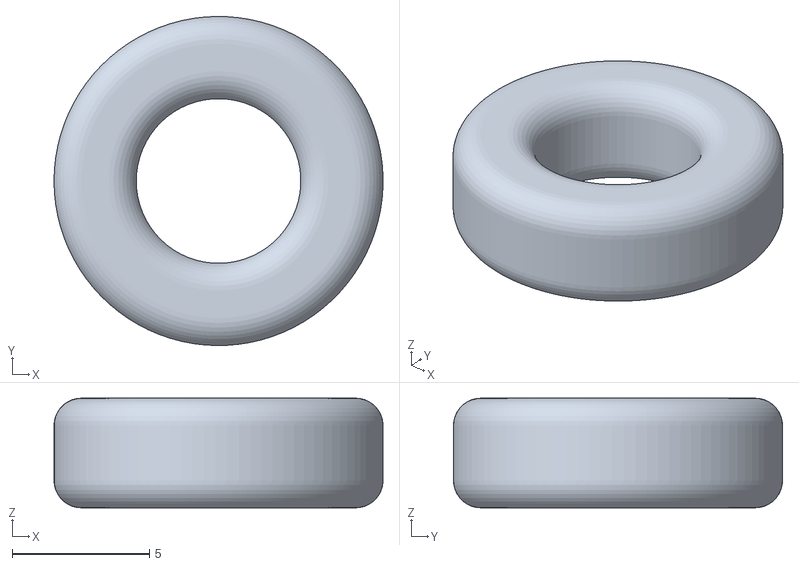
[picture p73: CAD file, 2020-08-17]
3D stuff/Torus.stl
12.0 x 12.0 x 4.00
