Fmulder007/Karat2N_synt/3D stuff/RTC_support.stl

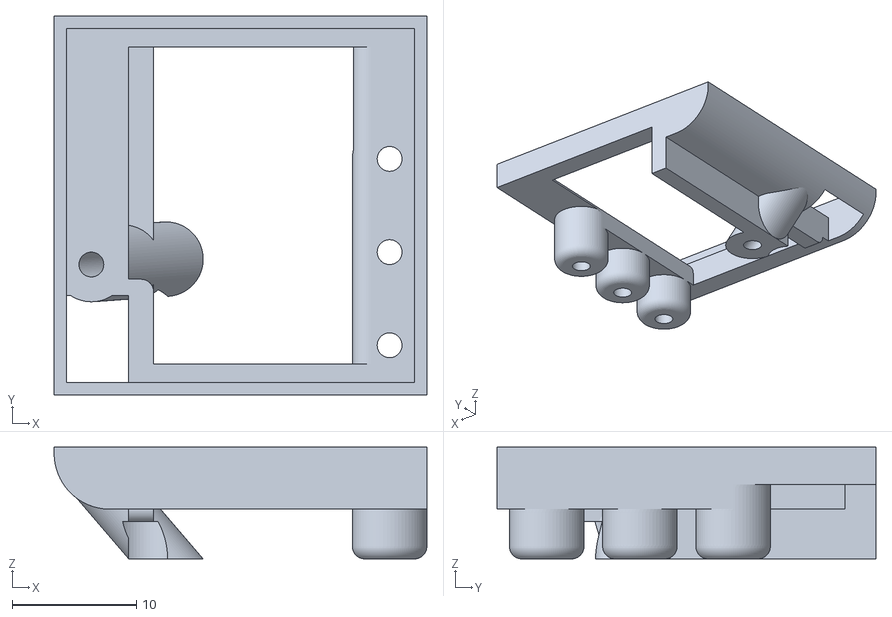
[picture p74: CAD file, 2020-08-13]
3D stuff/RTC_support.stl
30.0 x 30.5 x 9.00
