Fmulder007/Karat2N_synt/3D stuff/Conduktor.stl

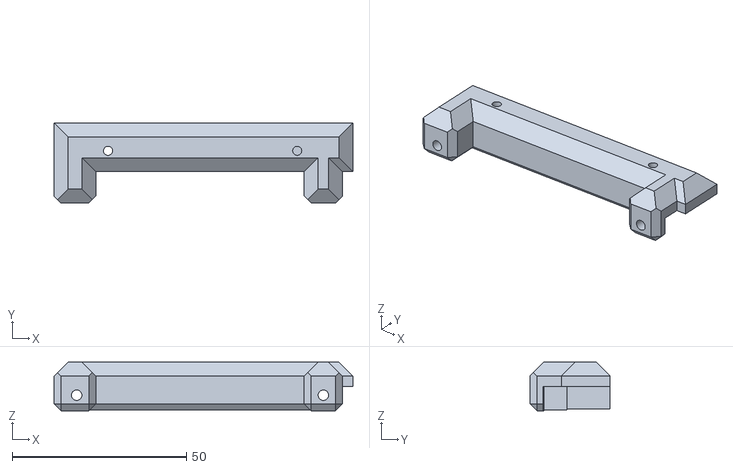
[picture p75: CAD file, 2020-08-13]
3D stuff/Conduktor.stl
85.8 x 23.0 x 14.0
