Fmulder007/Karat2N_synt/3D stuff/Karat-2N_display_support_2.stl

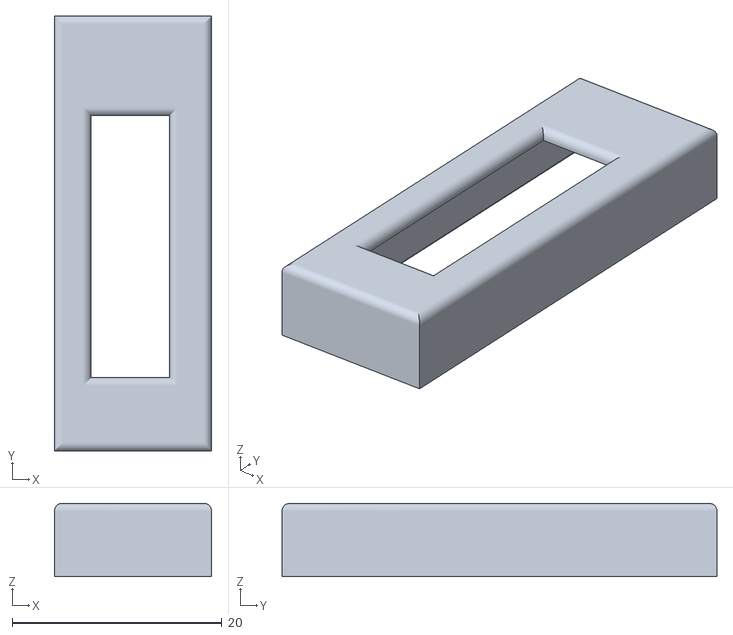
[picture p76: CAD file, 2020-08-02]
3D stuff/Karat-2N_display_support_2.stl
15.0 x 41.5 x 7.00
