Fmulder007/Karat2N_synt/3D stuff/Karat2_sintez_support1.stl

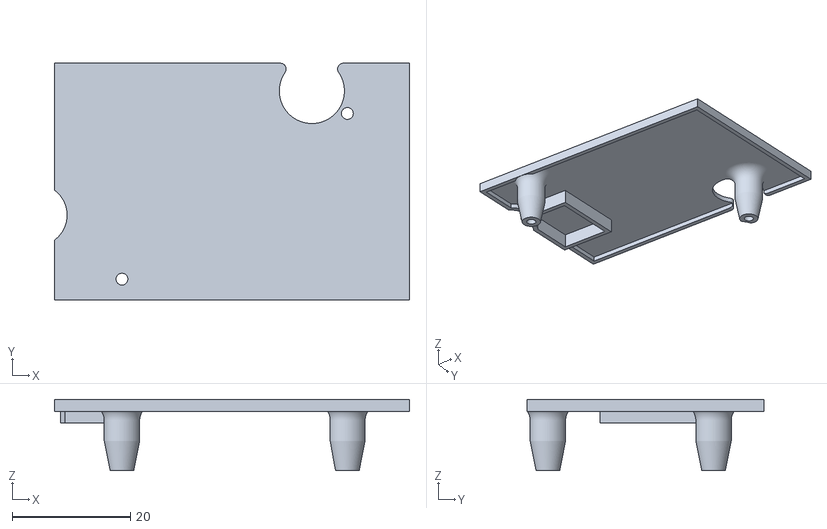
[picture p77: CAD file, 2020-08-02]
3D stuff/Karat2_sintez_support1.stl
60.0 x 40.0 x 12.0
