Fmulder007/Karat2N_synt/3D stuff/Knob1.stl

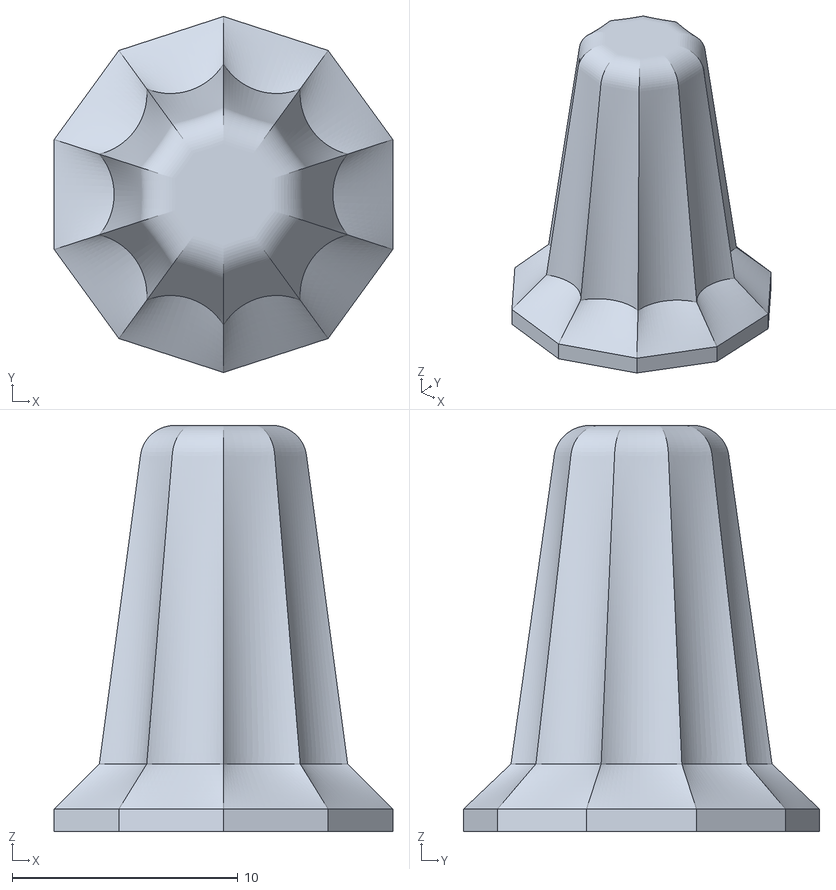
[picture p78: CAD file, 2020-08-02]
3D stuff/Knob1.stl
15.0 x 15.8 x 18.0
