Fmulder007/Karat2N_synt/3D stuff/Capacitor_Space.stl

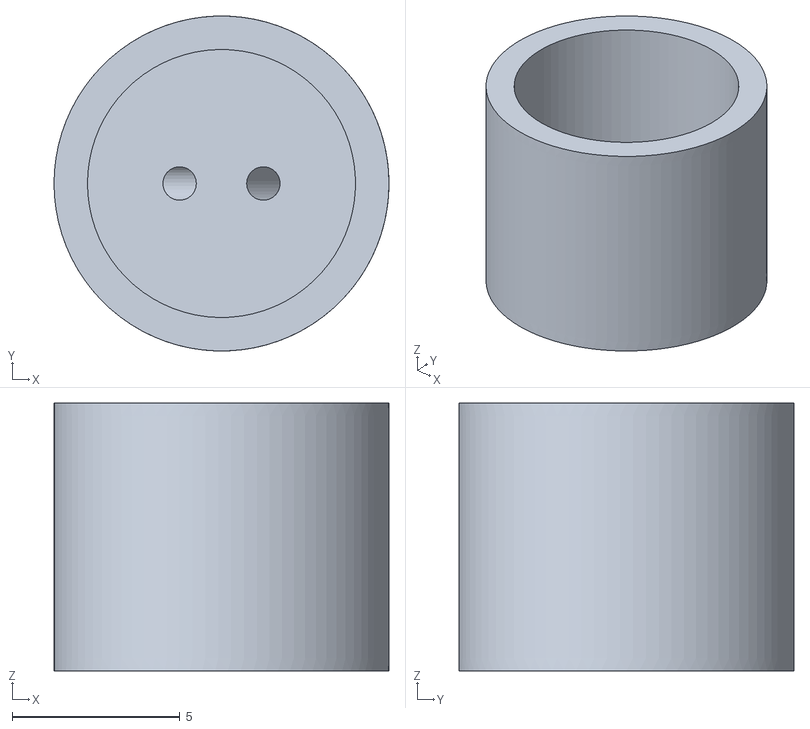
[picture p79: CAD file, 2020-07-16]
3D stuff/Capacitor_Space.stl
10.0 x 10.00 x 8.00
