Fmulder007/Karat2N_synt/3D stuff/Karat_Display_Support.stl

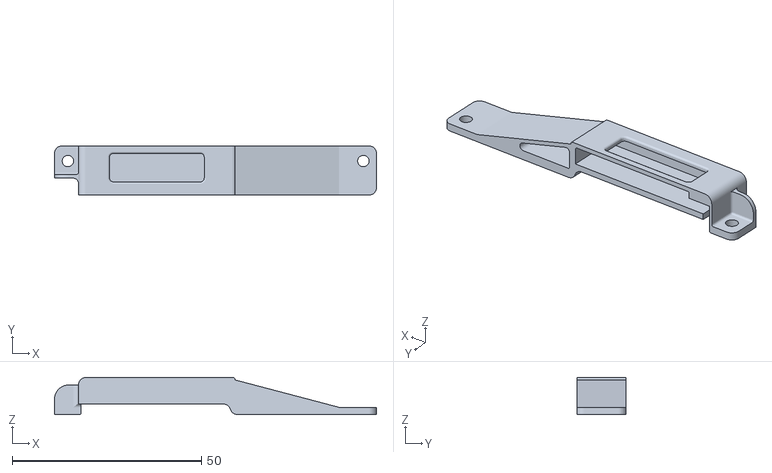
[picture p80: CAD file, 2020-06-26]
3D stuff/Karat_Display_Support.stl
85.0 x 13.0 x 9.80
